sahilvxky25/Self-Balancing-Bot---E-yantra/MANIPULATOR_NEW.stl

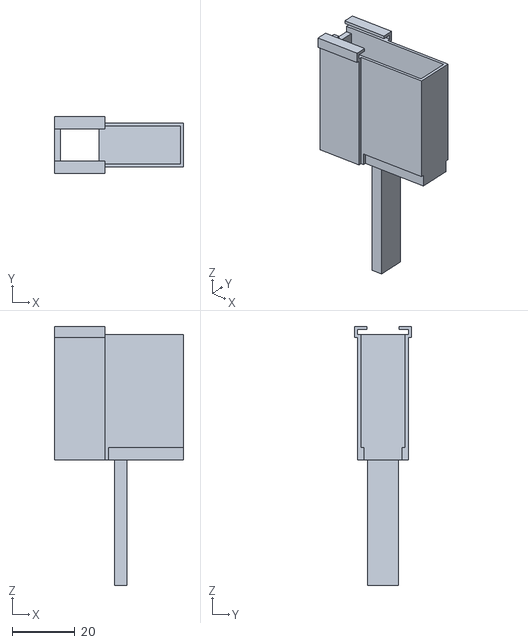
[picture p19: CAD file, 2026-01-01]
MANIPULATOR_NEW.stl
41.2 x 18.2 x 82.5
