sahilvxky25/Self-Balancing-Bot---E-yantra/GRIP.stl

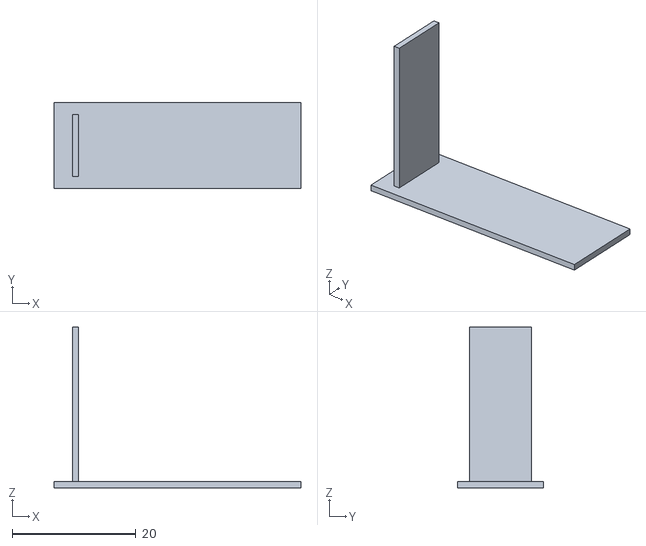
[picture p20: CAD file, 2026-01-01]
GRIP.stl
40.0 x 14.0 x 26.0
