sahilvxky25/Self-Balancing-Bot---E-yantra/gripper_1.stl

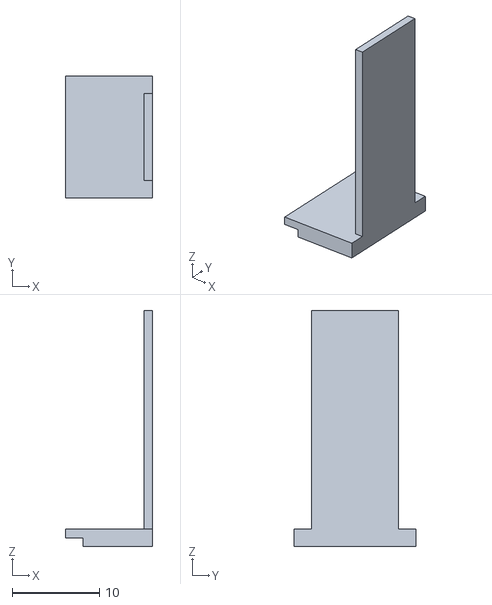
[picture p21: CAD file, 2025-12-06]
gripper_1.stl
10.0 x 14.0 x 27.0
