sahilvxky25/Self-Balancing-Bot---E-yantra/CAP.stl

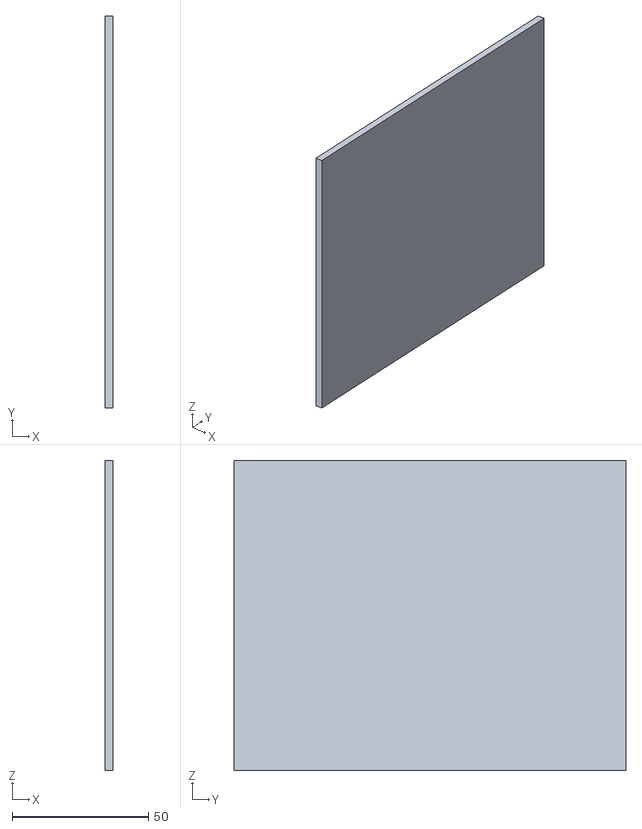
[picture p22: CAD file, 2025-12-06]
CAP.stl
3.00 x 144.0 x 114.0
