sahilvxky25/Self-Balancing-Bot---E-yantra/SHELF.stl

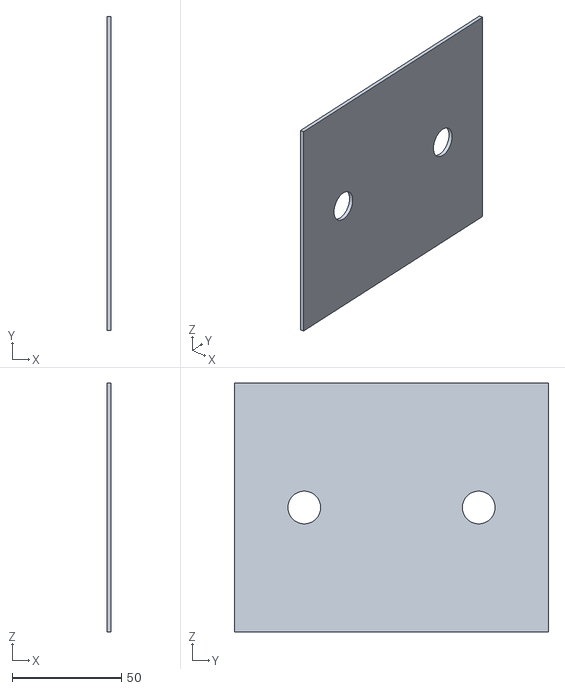
[picture p23: CAD file, 2025-12-06]
SHELF.stl
2.00 x 144.0 x 114.0
