sahilvxky25/Self-Balancing-Bot---E-yantra/gripper_2.stl

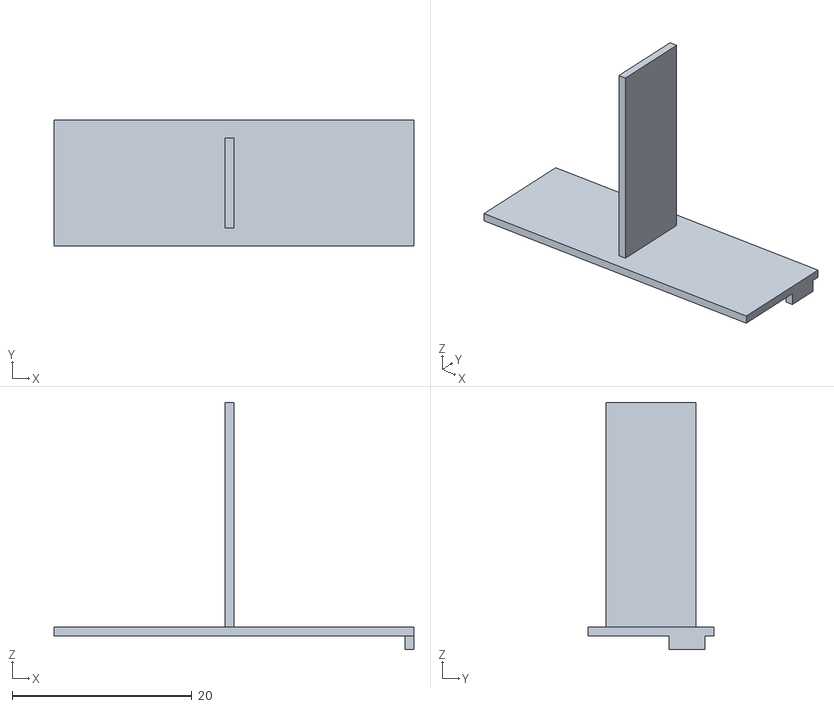
[picture p24: CAD file, 2025-12-06]
gripper_2.stl
40.0 x 14.0 x 27.5
