sahilvxky25/Self-Balancing-Bot---E-yantra/servo1_rack.stl

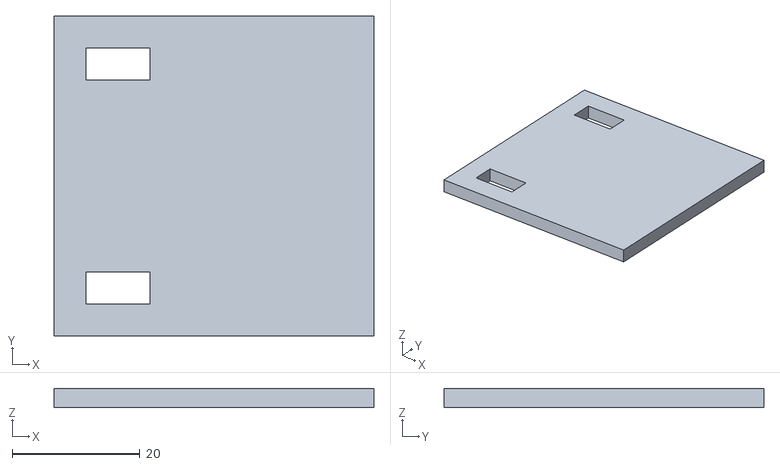
[picture p25: CAD file, 2025-12-06]
servo1_rack.stl
50.0 x 50.0 x 3.00
