sahilvxky25/Self-Balancing-Bot---E-yantra/Spur Gear (14 teeth).stl

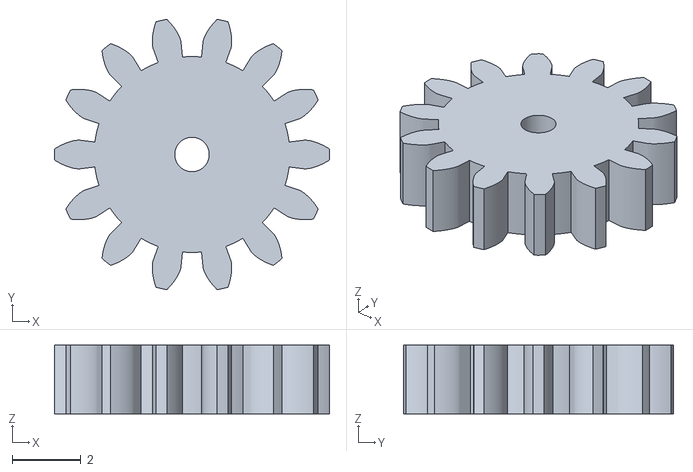
[picture p26: CAD file, 2025-12-06]
Spur Gear (14 teeth).stl
8.00 x 7.86 x 2.00
