sahilvxky25/Self-Balancing-Bot---E-yantra/gear_linear.stl

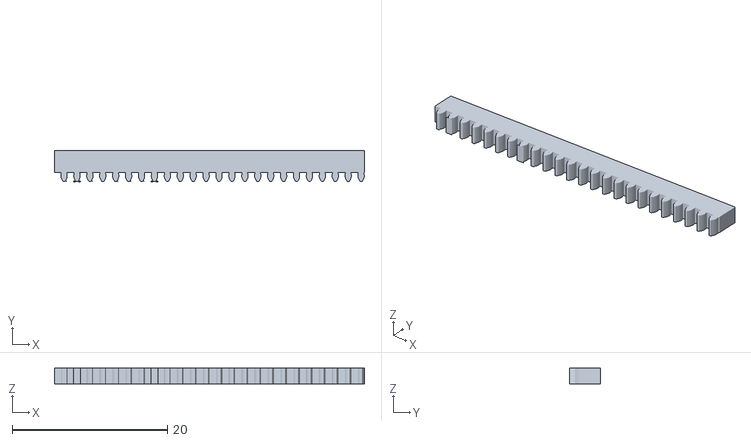
[picture p27: CAD file, 2025-12-06]
gear_linear.stl
40.0 x 4.00 x 2.00
