sahilvxky25/Self-Balancing-Bot---E-yantra/hinge.stl

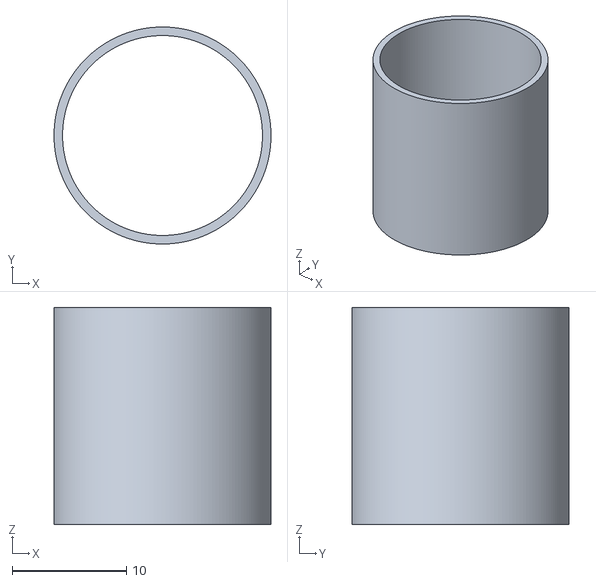
[picture p28: CAD file, 2025-12-06]
hinge.stl
19.0 x 19.0 x 19.0
