sahilvxky25/Self-Balancing-Bot---E-yantra/hinge holder.stl

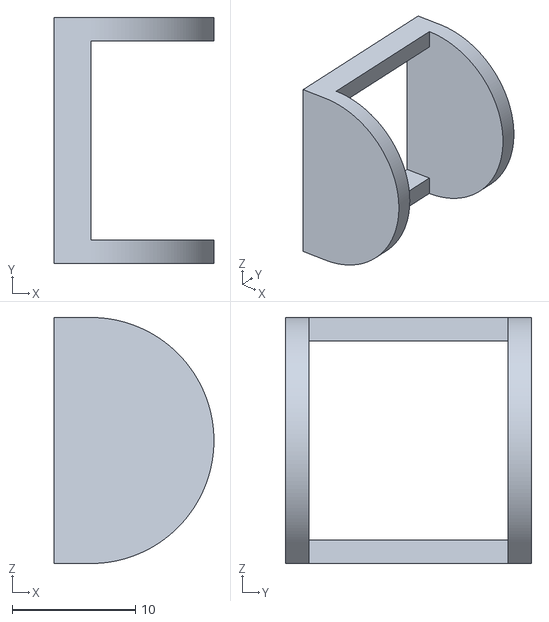
[picture p29: CAD file, 2025-12-06]
hinge holder.stl
13.0 x 20.0 x 20.0
