sahilvxky25/Self-Balancing-Bot---E-yantra/Obstacle_1.stl

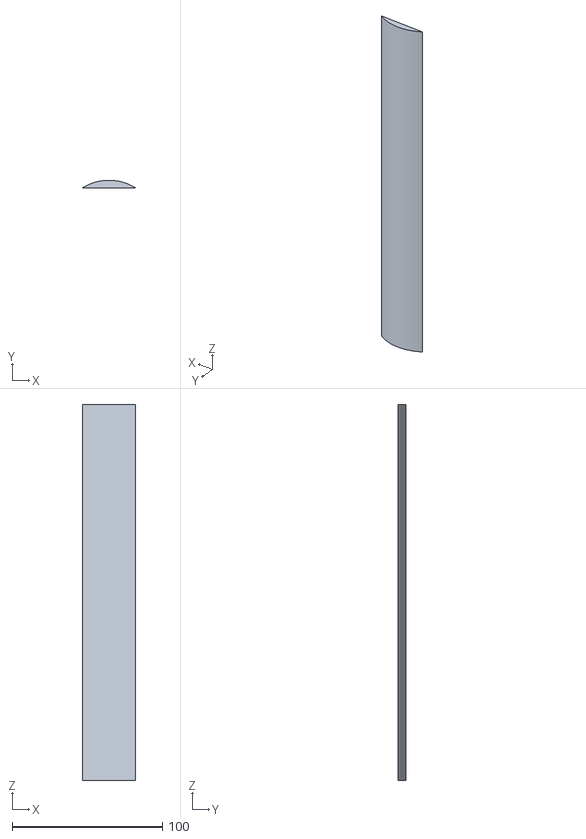
[picture p30: CAD file, 2025-11-24]
Obstacle_1.stl
35.0 x 5.00 x 250.0
