sahilvxky25/Self-Balancing-Bot---E-yantra/Gravel_Obstacle.stl

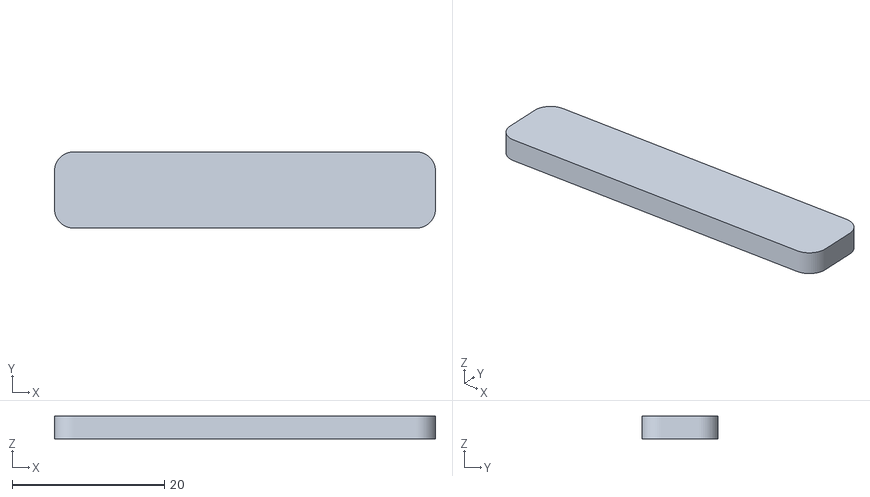
[picture p31: CAD file, 2025-11-24]
Gravel_Obstacle.stl
50.0 x 10.0 x 3.00
