sahilvxky25/Self-Balancing-Bot---E-yantra/ramp_obstacle.stl

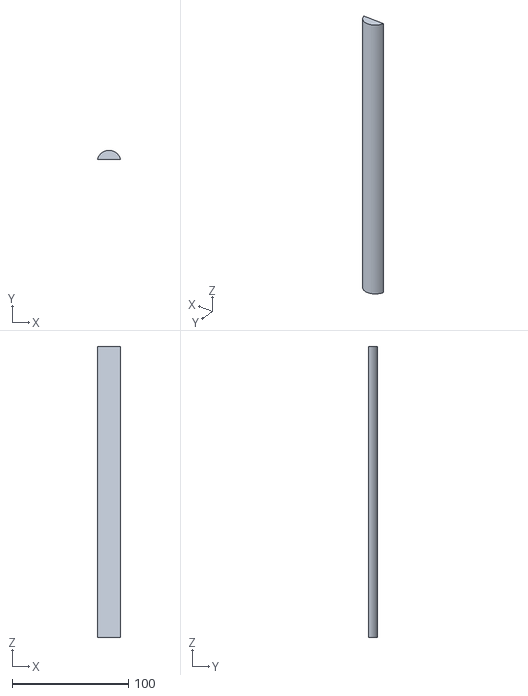
[picture p32: CAD file, 2025-11-24]
ramp_obstacle.stl
20.0 x 8.00 x 250.0
